SrSagan/IAuto/camera/square.bmp

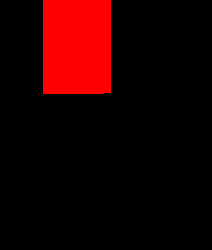
camera/square.bmp
