SrSagan/IAuto/robot/RB_OneWire.cpp

/*
Copyright (c) 2007, Jim Studt  (original old version - many contributors since)

The latest version of this library may be found at:
  http://www.pjrc.com/teensy/td_libs_OneWire.html

OneWire has been maintained by Paul Stoffregen (paul@pjrc.com) since
January 2010.

DO NOT EMAIL for technical support, especially not for ESP chips!
All project support questions must be posted on public forums
relevant to the board or chips used.  If using Arduino, post on
Arduino's forum.  If using ESP, post on the ESP community forums.
There is ABSOLUTELY NO TECH SUPPORT BY PRIVATE EMAIL!

Github's issue tracker for OneWire should be used only to report
specific bugs.  DO NOT request project support via Github.  All
project and tech support questions must be posted on forums, not
github issues.  If you experience a problem and you are not
absolutely sure it's an issue with the library, ask on a forum
first.  Only use github to report issues after experts have
confirmed the issue is with OneWire rather than your project.

Back in 2010, OneWire was in need of many bug fixes, but had
been abandoned the original author (Jim Studt).  None of the known
contributors were interested in maintaining OneWire.  Paul typically
works on OneWire every 6 to 12 months.  Patches usually wait that
long.  If anyone is interested in more actively maintaining OneWire,
please contact Paul (this is pretty much the only reason to use
private email about OneWire).

OneWire is now very mature code.  No changes other than adding
definitions for newer hardware support are anticipated.

Version 2.3:
  Unknown chip fallback mode, Roger Clark
  Teensy-LC compatibility, Paul Stoffregen
  Search bug fix, Love Nystrom

Version 2.2:
  Teensy 3.0 compatibility, Paul Stoffregen, paul@pjrc.com
  Arduino Due compatibility, http://arduino.cc/forum/index.php?topic=141030
  Fix DS18B20 example negative temperature
  Fix DS18B20 example's low res modes, Ken Butcher
  Improve reset timing, Mark Tillotson
  Add const qualifiers, Bertrik Sikken
  Add initial value input to crc16, Bertrik Sikken
  Add target_search() function, Scott Roberts

Version 2.1:
  Arduino 1.0 compatibility, Paul Stoffregen
  Improve temperature example, Paul Stoffregen
  DS250x_PROM example, Guillermo Lovato
  PIC32 (chipKit) compatibility, Jason Dangel, dangel.jason AT gmail.com
  Improvements from Glenn Trewitt:
  - crc16() now works
  - check_crc16() does all of calculation/checking work.
  - Added read_bytes() and write_bytes(), to reduce tedious loops.
  - Added ds2408 example.
  Delete very old, out-of-date readme file (info is here)

Version 2.0: Modifications by Paul Stoffregen, January 2010:
http://www.pjrc.com/teensy/td_libs_OneWire.html
  Search fix from Robin James
    http://www.arduino.cc/cgi-bin/yabb2/YaBB.pl?num=1238032295/27#27
  Use direct optimized I/O in all cases
  Disable interrupts during timing critical sections
    (this solves many random communication errors)
  Disable interrupts during read-modify-write I/O
  Reduce RAM consumption by eliminating unnecessary
    variables and trimming many to 8 bits
  Optimize both crc8 - table version moved to flash

Modified to work with larger numbers of devices - avoids loop.
Tested in Arduino 11 alpha with 12 sensors.
26 Sept 2008 -- Robin James
http://www.arduino.cc/cgi-bin/yabb2/YaBB.pl?num=1238032295/27#27

Updated to work with arduino-0008 and to include skip() as of
2007/07/06. --RJL20

Modified to calculate the 8-bit CRC directly, avoiding the need for
the 256-byte lookup table to be loaded in RAM.  Tested in arduino-0010
-- Tom Pollard, Jan 23, 2008

Jim Studt's original library was modified by Josh Larios.

Tom Pollard, pollard@alum.mit.edu, contributed around May 20, 2008

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
Much of the code was inspired by Derek Yerger's code, though I don't
think much of that remains.  In any event that was..
    (copyleft) 2006 by Derek Yerger - Free to distribute freely.

The CRC code was excerpted and inspired by the Dallas Semiconductor
sample code bearing this copyright.
//---------------------------------------------------------------------------
// Copyright (C) 2000 Dallas Semiconductor Corporation, All Rights Reserved.
//
// Permission is hereby granted, free of charge, to any person obtaining a
// copy of this software and associated documentation files (the "Software"),
// to deal in the Software without restriction, including without limitation
// the rights to use, copy, modify, merge, publish, distribute, sublicense,
// and/or sell copies of the Software, and to permit persons to whom the
// Software is furnished to do so, subject to the following conditions:
//
// The above copyright notice and this permission notice shall be included
// in all copies or substantial portions of the Software.
//
// THE SOFTWARE IS PROVIDED "AS IS", WITHOUT WARRANTY OF ANY KIND, EXPRESS
// OR IMPLIED, INCLUDING BUT NOT LIMITED TO THE WARRANTIES OF
// MERCHANTABILITY,  FITNESS FOR A PARTICULAR PURPOSE AND NONINFRINGEMENT.
// IN NO EVENT SHALL DALLAS SEMICONDUCTOR BE LIABLE FOR ANY CLAIM, DAMAGES
// OR OTHER LIABILITY, WHETHER IN AN ACTION OF CONTRACT, TORT OR OTHERWISE,
// ARISING FROM, OUT OF OR IN CONNECTION WITH THE SOFTWARE OR THE USE OR
// OTHER DEALINGS IN THE SOFTWARE.
//
// Except as contained in this notice, the name of Dallas Semiconductor
// shall not be used except as stated in the Dallas Semiconductor
// Branding Policy.
//--------------------------------------------------------------------------
*/

#include <Arduino.h>
#include "RB_OneWire.h"
#include "OneWire_direct_gpio.h"


RB_OneWire::RB_OneWire(void)
{
	
	
}
RB_OneWire::RB_OneWire(uint8_t pin)
{
	bitmask = PIN_TO_BITMASK(pin);
	baseReg = PIN_TO_BASEREG(pin);
	
}

void RB_OneWire::reset(uint8_t pin)
{
  bitmask = PIN_TO_BITMASK(pin);
  baseReg = PIN_TO_BASEREG(pin);
}

// Perform the onewire reset function.  We will wait up to 250uS for
// the bus to come high, if it doesn't then it is broken or shorted
// and we return a 0;
//
// Returns 1 if a device asserted a presence pulse, 0 otherwise.
//

bool RB_OneWire::readIO(void)
{
  IO_REG_TYPE           mask = bitmask;
  volatile IO_REG_TYPE *reg IO_REG_BASE_ATTR = baseReg;
  uint8_t r;
  DIRECT_MODE_INPUT(reg, mask);    // allow it to float
  delayMicroseconds(10);
  r = DIRECT_READ(reg, mask);
  return(r);
}


uint8_t RB_OneWire::reset(void)
{
	IO_REG_TYPE mask IO_REG_MASK_ATTR = bitmask;
	volatile IO_REG_TYPE *reg IO_REG_BASE_ATTR = baseReg;
	uint8_t r;
	uint8_t retries = 125;

	noInterrupts();
	DIRECT_MODE_INPUT(reg, mask);
	interrupts();
	// wait until the wire is high... just in case
	do {
		if (--retries == 0) return 0;
		delayMicroseconds(2);
	} while ( !DIRECT_READ(reg, mask));

	noInterrupts();
	DIRECT_WRITE_LOW(reg, mask);
	DIRECT_MODE_OUTPUT(reg, mask);	// drive output low
	interrupts();
	delayMicroseconds(480);
	noInterrupts();
	DIRECT_MODE_INPUT(reg, mask);	// allow it to float
	delayMicroseconds(70);
	r = !DIRECT_READ(reg, mask);
	interrupts();
	delayMicroseconds(410);
	return r;
}

//
// Write a bit. Port and bit is used to cut lookup time and provide
// more certain timing.
//
void RB_OneWire::write_bit(uint8_t v)
{
	IO_REG_TYPE mask IO_REG_MASK_ATTR = bitmask;
	volatile IO_REG_TYPE *reg IO_REG_BASE_ATTR = baseReg;

	if (v & 1) {
		noInterrupts();
		DIRECT_WRITE_LOW(reg, mask);
		DIRECT_MODE_OUTPUT(reg, mask);	// drive output low
		delayMicroseconds(10);
		DIRECT_WRITE_HIGH(reg, mask);	// drive output high
		interrupts();
		delayMicroseconds(55);
	} else {
		noInterrupts();
		DIRECT_WRITE_LOW(reg, mask);
		DIRECT_MODE_OUTPUT(reg, mask);	// drive output low
		delayMicroseconds(65);
		DIRECT_WRITE_HIGH(reg, mask);	// drive output high
		interrupts();
		delayMicroseconds(5);
	}
}

//
// Read a bit. Port and bit is used to cut lookup time and provide
// more certain timing.
//
uint8_t RB_OneWire::read_bit(void)
{
	IO_REG_TYPE mask IO_REG_MASK_ATTR = bitmask;
	volatile IO_REG_TYPE *reg IO_REG_BASE_ATTR = baseReg;
	uint8_t r;

	noInterrupts();
	DIRECT_MODE_OUTPUT(reg, mask);
	DIRECT_WRITE_LOW(reg, mask);
	delayMicroseconds(3);
	DIRECT_MODE_INPUT(reg, mask);	// let pin float, pull up will raise
	delayMicroseconds(10);
	r = DIRECT_READ(reg, mask);
	interrupts();
	delayMicroseconds(53);
	return r;
}

//
// Write a byte. The writing code uses the active drivers to raise the
// pin high, if you need power after the write (e.g. DS18S20 in
// parasite power mode) then set 'power' to 1, otherwise the pin will
// go tri-state at the end of the write to avoid heating in a short or
// other mishap.
//
void RB_OneWire::write(uint8_t v, uint8_t power /* = 0 */) {
    uint8_t bitMask;

    for (bitMask = 0x01; bitMask; bitMask <<= 1) {
	RB_OneWire::write_bit( (bitMask & v)?1:0);
    }
    if ( !power) {
	noInterrupts();
	DIRECT_MODE_INPUT(baseReg, bitmask);
	DIRECT_WRITE_LOW(baseReg, bitmask);
	interrupts();
    }
}

void RB_OneWire::write_bytes(const uint8_t *buf, uint16_t count, bool power /* = 0 */) {
  for (uint16_t i = 0 ; i < count ; i++)
    write(buf[i]);
  if (!power) {
    noInterrupts();
    DIRECT_MODE_INPUT(baseReg, bitmask);
    DIRECT_WRITE_LOW(baseReg, bitmask);
    interrupts();
  }
}

//
// Read a byte
//
uint8_t RB_OneWire::read() {
    uint8_t bitMask;
    uint8_t r = 0;

    for (bitMask = 0x01; bitMask; bitMask <<= 1) {
	if ( RB_OneWire::read_bit()) r |= bitMask;
    }
    return r;
}

void RB_OneWire::read_bytes(uint8_t *buf, uint16_t count) {
  for (uint16_t i = 0 ; i < count ; i++)
    buf[i] = read();
}

//
// Do a ROM select
//
void RB_OneWire::select(const uint8_t rom[8])
{
    uint8_t i;

    write(0x55);           // Choose ROM

    for (i = 0; i < 8; i++) write(rom[i]);
}

//
// Do a ROM skip
//
void RB_OneWire::skip()
{
    write(0xCC);           // Skip ROM
}

void RB_OneWire::depower()
{
	noInterrupts();
	DIRECT_MODE_INPUT(baseReg, bitmask);
	interrupts();
}
